NarenOO3/HolaBot/Design Files/3D render of Design 1.jpeg

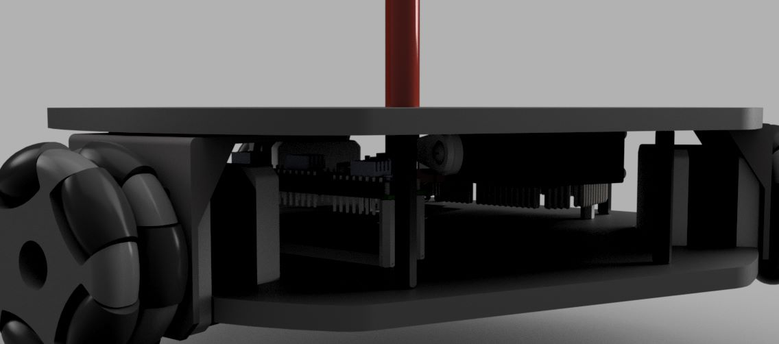
Design Files/3D render of Design 1.jpeg
