NarenOO3/HolaBot/Design Files/3D render of Design 2.png

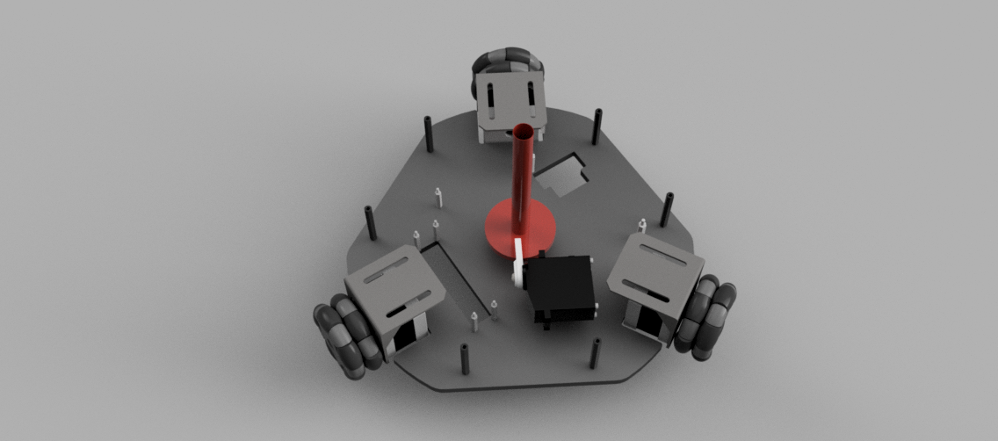
Design Files/3D render of Design 2.png
