NarenOO3/HolaBot/Design Files/3D render of Design 6.jpeg

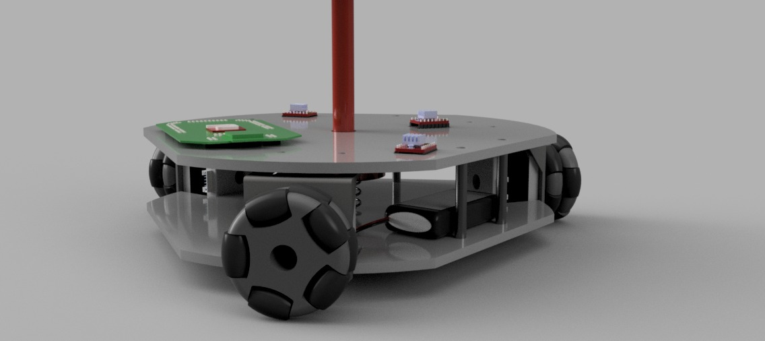
Design Files/3D render of Design 6.jpeg
