NarenOO3/HolaBot/Design Files/Centre Hole Diameter.png

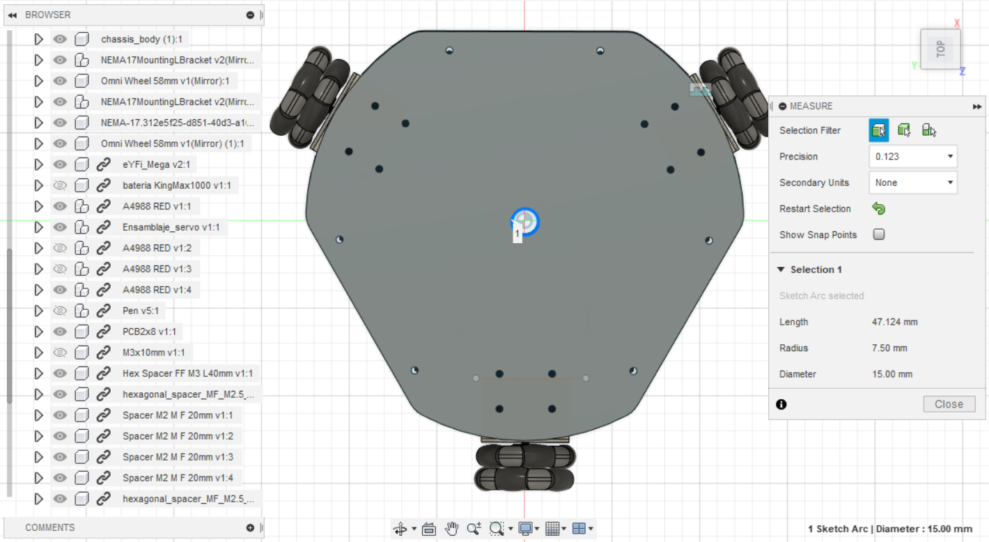
Design Files/Centre Hole Diameter.png
