NarenOO3/HolaBot/Task Files/Task 4b/Chassis body final new v23.png

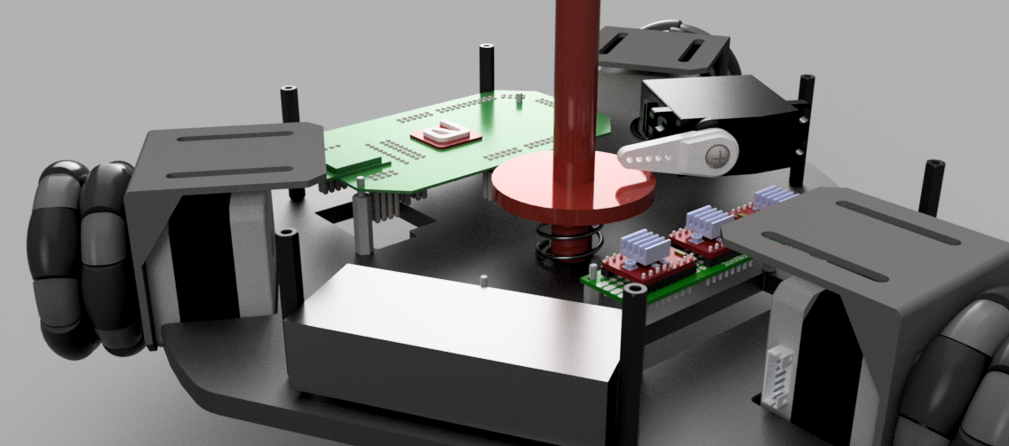
Task Files/Task 4b/Chassis body final new v23.png
