NarenOO3/HolaBot/Task Files/Task 4b/Circle Frame 1.png

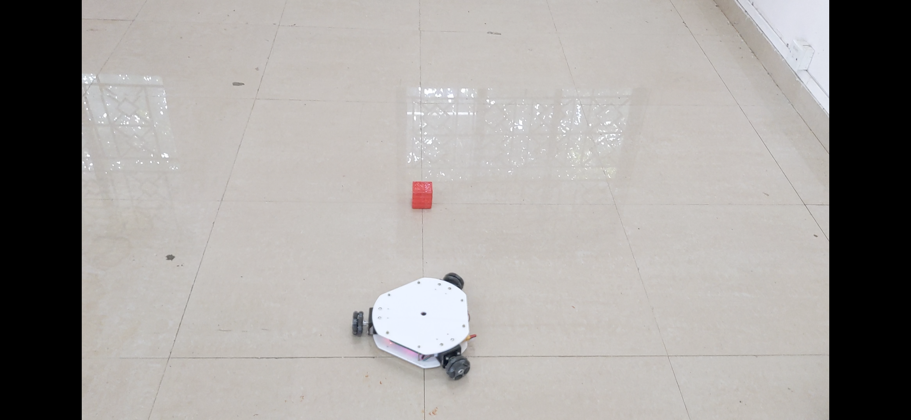
Task Files/Task 4b/Circle Frame 1.png
