NarenOO3/HolaBot/Task Files/Task 4b/eyfi AVR Mega Pinout.png

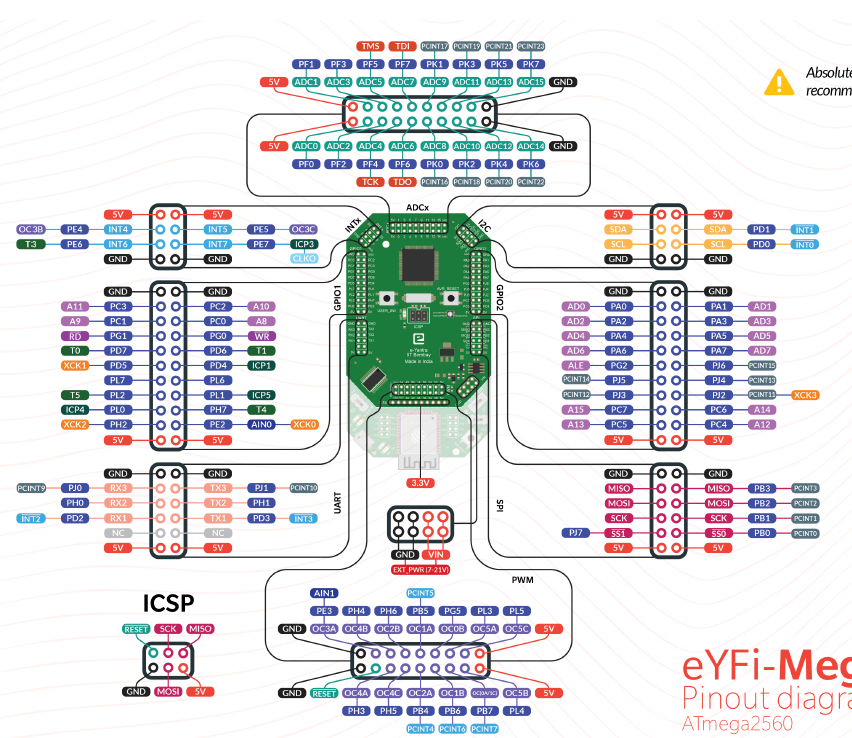
Task Files/Task 4b/eyfi AVR Mega Pinout.png
