NarenOO3/HolaBot/Task Files/Task 4b/L frame 1.png

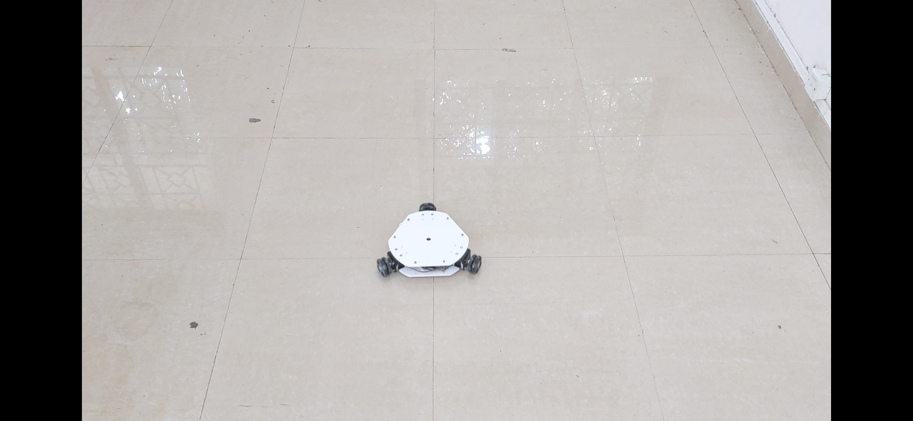
Task Files/Task 4b/L frame 1.png
