NarenOO3/HolaBot/Task Files/Task 4b/millis approah for multiple stepper motor.png

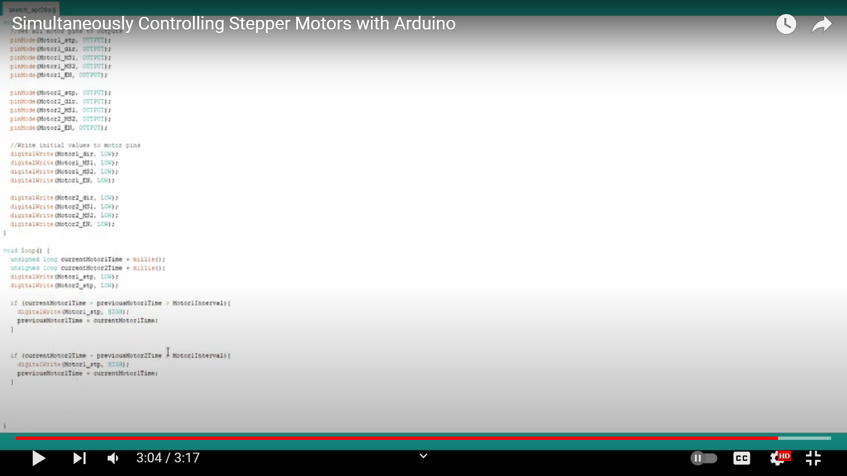
Task Files/Task 4b/millis approah for multiple stepper motor.png
