NarenOO3/HolaBot/Task Files/Task 5/arena hola.png

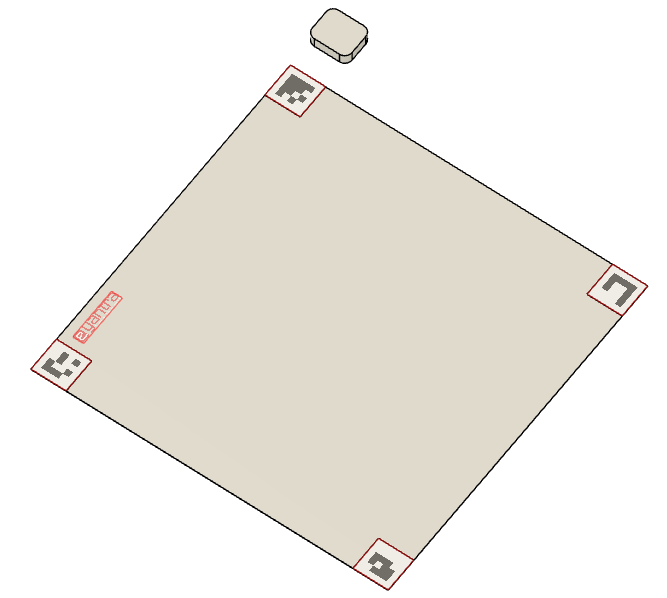
Task Files/Task 5/arena hola.png
