NarenOO3/HolaBot/Design Files/Final Assembled Bot.jpeg

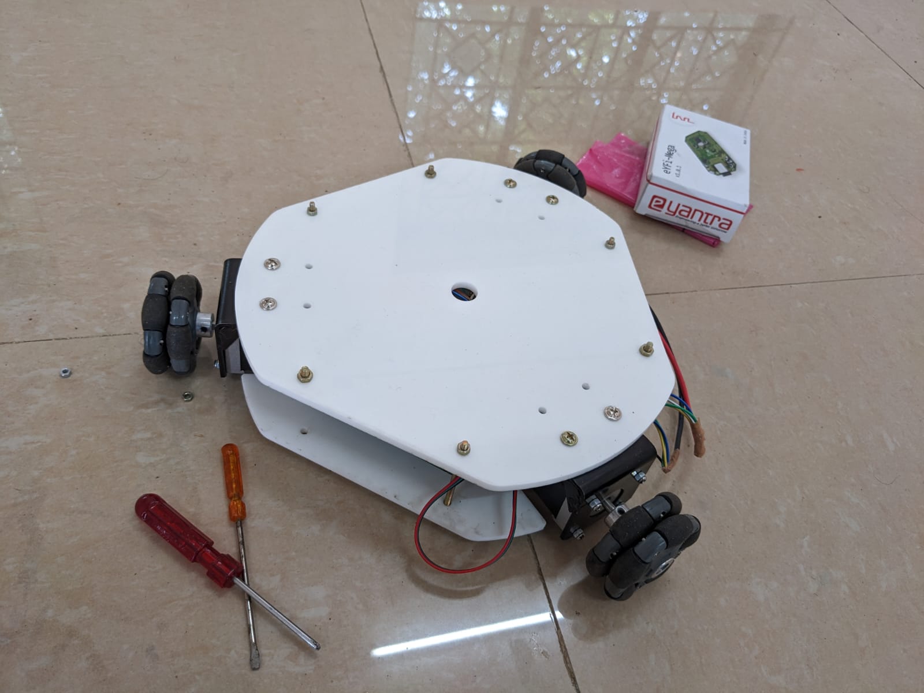
Design Files/Final Assembled Bot.jpeg
